nuzubab/Object-Detection-PCB/333.jpg

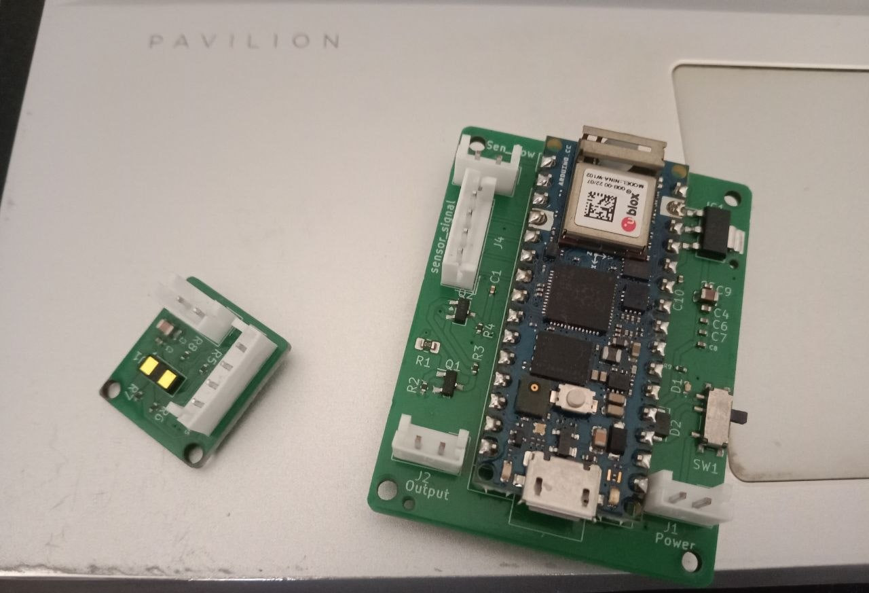
333.jpg
